poetaster/scarp/firmware/Pikobeats/filter.h

#define LPF_MAX 45

int32_t x1_f, x2_f, y1_f, y2_f;

uint8_t filter_lpf(int32_t x, int32_t f_, uint8_t q) {
  int32_t y;
  uint8_t f = f_;
  if (f_ < 0) {
    f = 0;
  }

  if (f > LPF_MAX) f = LPF_MAX;
  if (f == 0) {
    y = 3984 * x + 7968 * x1_f + 3984 * x2_f - -2009486 * y1_f - 976845 * y2_f;
  } else if (f == 1) {
    y = 4462 * x + 8924 * x1_f + 4462 * x2_f - -2003486 * y1_f - 972758 * y2_f;
  } else if (f == 2) {
    y = 4997 * x + 9993 * x1_f + 4997 * x2_f - -1997039 * y1_f - 968450 * y2_f;
  } else if (f == 3) {
    y = 5595 * x + 11190 * x1_f + 5595 * x2_f - -1990107 * y1_f - 963911 * y2_f;
  } else if (f == 4) {
    y = 6264 * x + 12527 * x1_f + 6264 * x2_f - -1982651 * y1_f - 959130 * y2_f;
  } else if (f == 5) {
    y = 7011 * x + 14023 * x1_f + 7011 * x2_f - -1974628 * y1_f - 954097 * y2_f;
  } else if (f == 6) {
    y = 7847 * x + 15694 * x1_f + 7847 * x2_f - -1965989 * y1_f - 948801 * y2_f;
  } else if (f == 7) {
    y = 8780 * x + 17561 * x1_f + 8780 * x2_f - -1956685 * y1_f - 943231 * y2_f;
  } else if (f == 8) {
    y = 9823 * x + 19646 * x1_f + 9823 * x2_f - -1946658 * y1_f - 937375 * y2_f;
  } else if (f == 9) {
    y = 10988 * x + 21975 * x1_f + 10988 * x2_f - -1935849 * y1_f -
        931223 * y2_f;
  } else if (f == 10) {
    y = 12287 * x + 24575 * x1_f + 12287 * x2_f - -1924191 * y1_f -
        924764 * y2_f;
  } else if (f == 11) {
    y = 13738 * x + 27475 * x1_f + 13738 * x2_f - -1911611 * y1_f -
        917986 * y2_f;
  } else if (f == 12) {
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
        207031 * yh2_f;
  } else if (f == 44) {
    y = 184162 * x + -368324 * xh1_f + 184162 * xh2_f - 541645 * yh1_f -
        229717 * yh2_f;
  } else if (f == 45) {
    y = 154430 * x + -308860 * xh1_f + 154430 * xh2_f - 692735 * yh1_f -
        261879 * yh2_f;
  } else if (f == 46) {
    y = 124774 * x + -249549 * xh1_f + 124774 * xh2_f - 855346 * yh1_f -
        305867 * yh2_f;
  } else if (f == 47) {
    y = 95593 * x + -191186 * xh1_f + 95593 * xh2_f - 1031049 * yh1_f -
        364844 * yh2_f;
  } else if (f == 48) {
    y = 67522 * x + -135044 * xh1_f + 67522 * xh2_f - 1221641 * yh1_f -
        443154 * yh2_f;
  } else {
    y = 41597 * x + -83194 * xh1_f + 41597 * xh2_f - 1429070 * yh1_f -
        546881 * yh2_f;
  }
  y = y >> 20;

  xh2_f = xh1_f;
  xh1_f = x;
  yh2_f = yh1_f;
  yh1_f = y;
  return (uint8_t)(y);
}
